MAIK97MAX/smartpowerbank2026/docs/images/i2c-bus.png

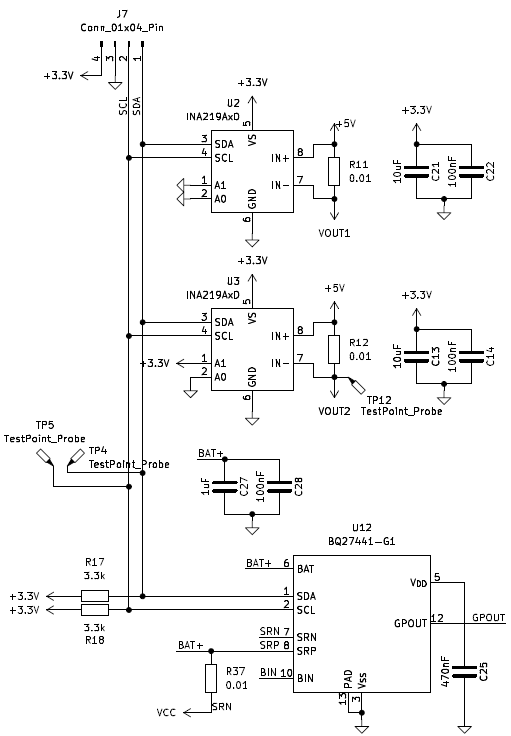
docs/images/i2c-bus.png
